aberardinelli/bourbondox/case/v2/right_plate.dxf

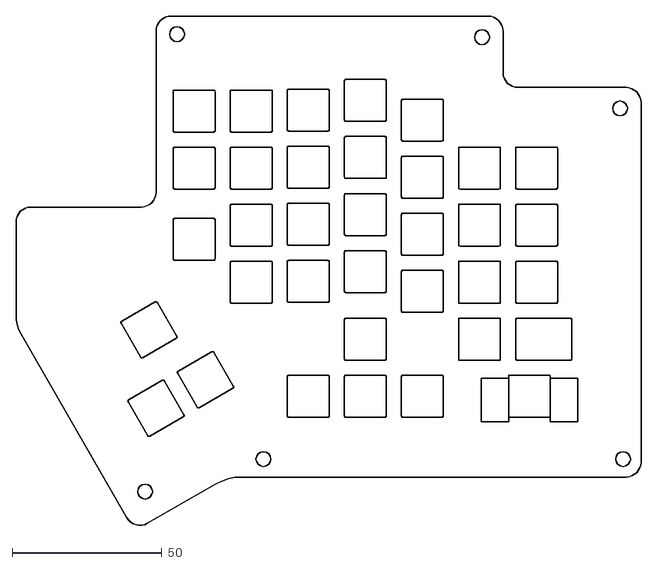
[picture p27: CAD file, 2021-11-10, an earlier design]
case/v2/right_plate.dxf
208.6 x 170.1
